kai-duchane/Power-Distribution-Board/02_Full-Distribution Board.kicad_sch

## KiCad design 02_Full-Distribution Board.kicad_sch (2025-08-18)

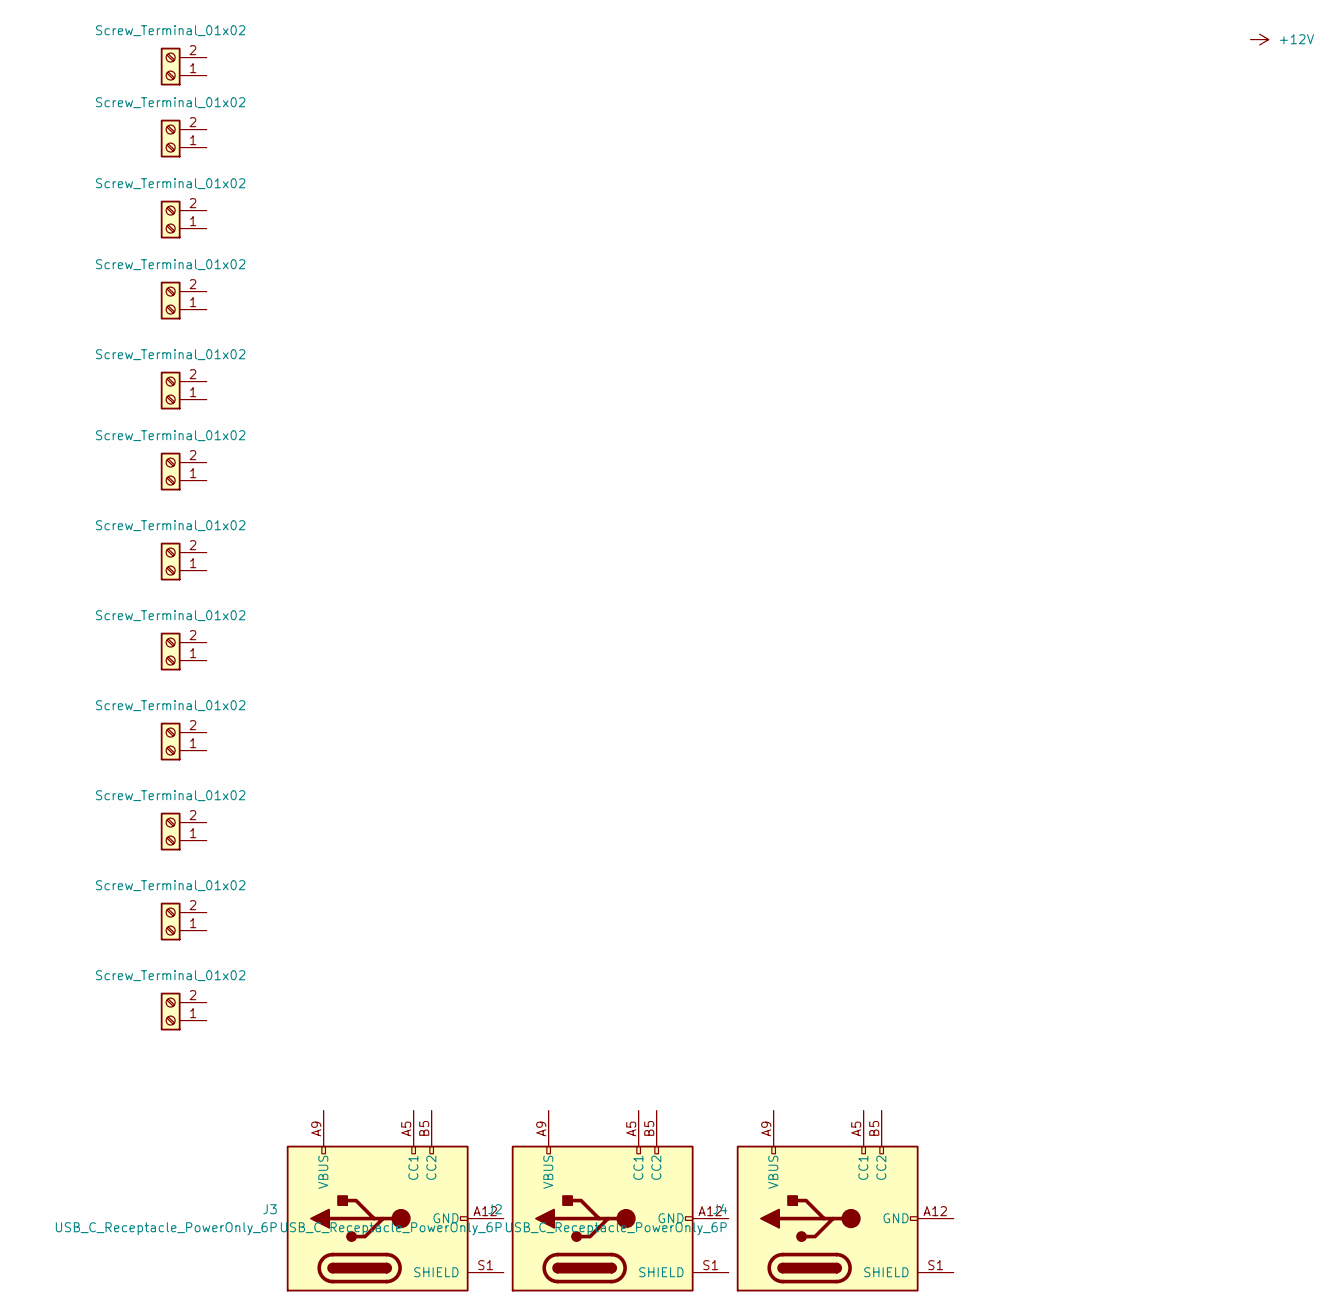
[picture p6: schematic 02_Full-Distribution Board.kicad_sch]

Parts:
J1, J6, J7, J8, J9, J10, J11, J12, J13, J14, J15, J16: Screw_Terminal_01x02
J2, J3, J4: USB_C_Receptacle_PowerOnly_6P

Connections:
unnamed: J2.A9 (VBUS), J2.B9 (VBUS)
unnamed: J2.A12 (GND), J2.B12 (GND)
unnamed: J3.A9 (VBUS), J3.B9 (VBUS)
unnamed: J3.A12 (GND), J3.B12 (GND)
unnamed: J4.A9 (VBUS), J4.B9 (VBUS)
unnamed: J4.A12 (GND), J4.B12 (GND)
